rashwinr/WISE/matlab/IEEE_sensors/data_matched/LA,LF,RA,RF/Y/60_down_final.jpg

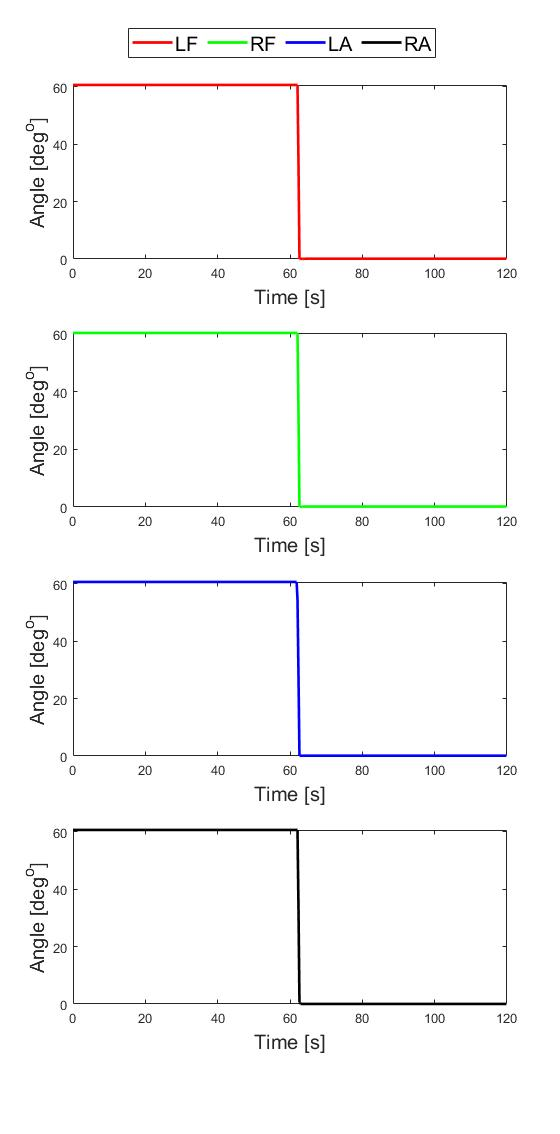
matlab/IEEE_sensors/data_matched/LA,LF,RA,RF/Y/60_down_final.jpg
