rashwinr/WISE/matlab/IEEE_sensors/data_matched/LA,LF,RA,RF/Y/80_up_final.jpg

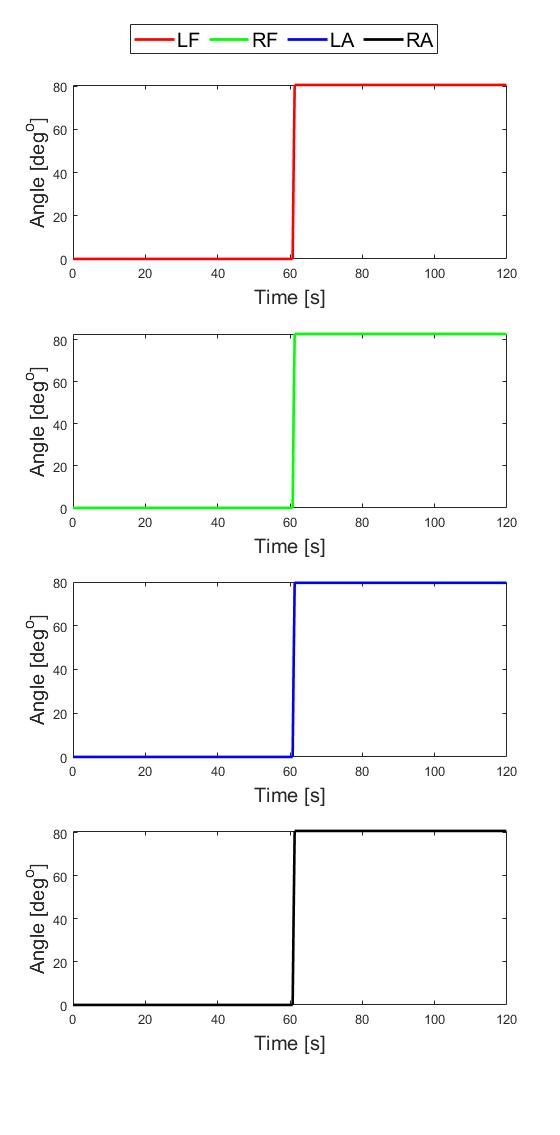
matlab/IEEE_sensors/data_matched/LA,LF,RA,RF/Y/80_up_final.jpg
