rashwinr/WISE/matlab/IEEE_sensors/data_matched/LA,LF,RA,RF/Y/final_0_mp.png

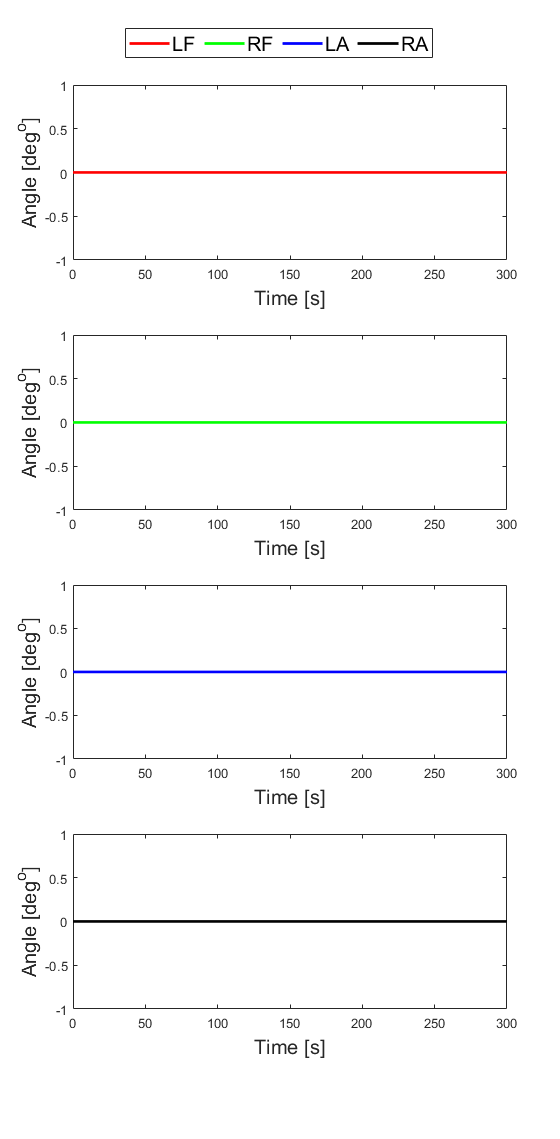
matlab/IEEE_sensors/data_matched/LA,LF,RA,RF/Y/final_0_mp.png
