rashwinr/WISE/matlab/IEEE_sensors/data_matched/LA,LF,RA,RF/Y/final_0degrees.jpg

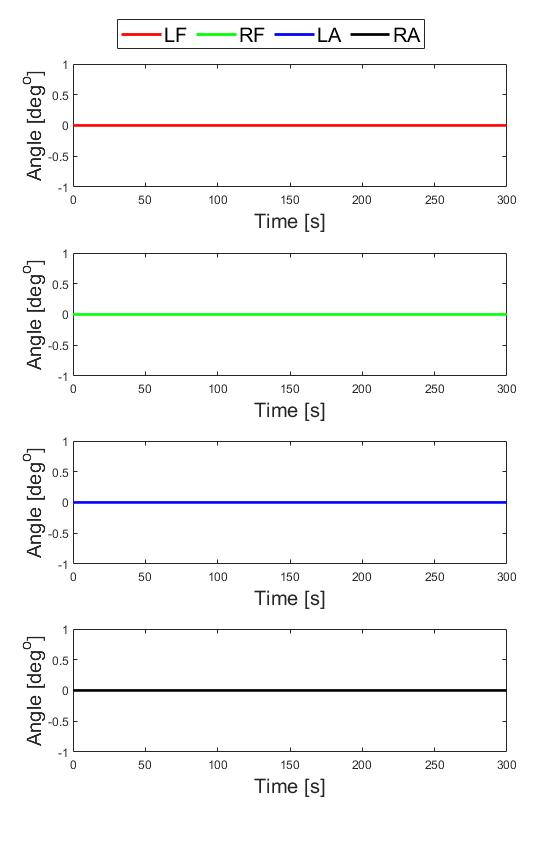
matlab/IEEE_sensors/data_matched/LA,LF,RA,RF/Y/final_0degrees.jpg
