rashwinr/WISE/matlab/IEEE_sensors/data_matched/LA,LF,RA,RF/Y/final_4comments.jpg

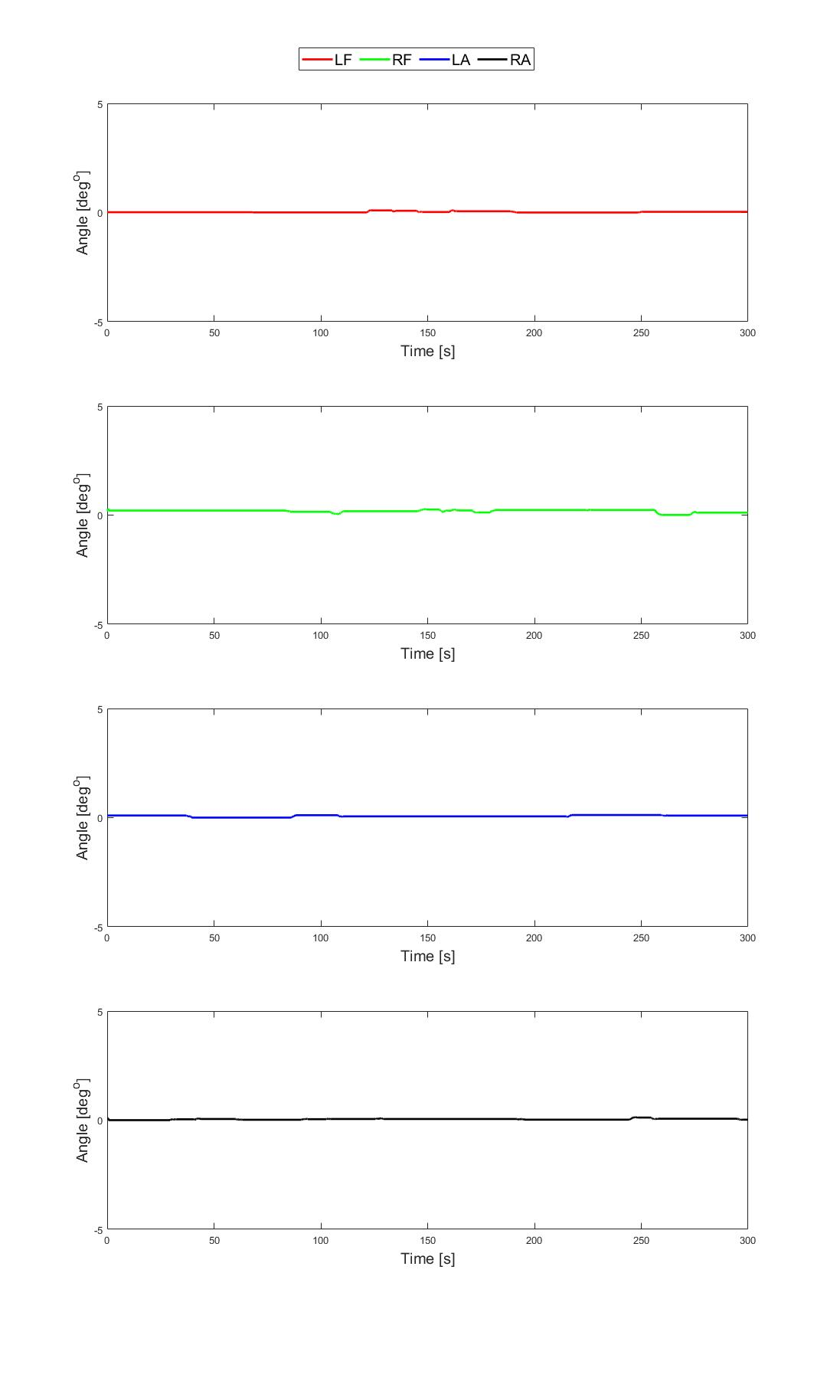
matlab/IEEE_sensors/data_matched/LA,LF,RA,RF/Y/final_4comments.jpg
