rashwinr/WISE/matlab/IEEE_sensors/data_matched/LA,LF,RA,RF/Y/final_4comments_-1to1.jpg

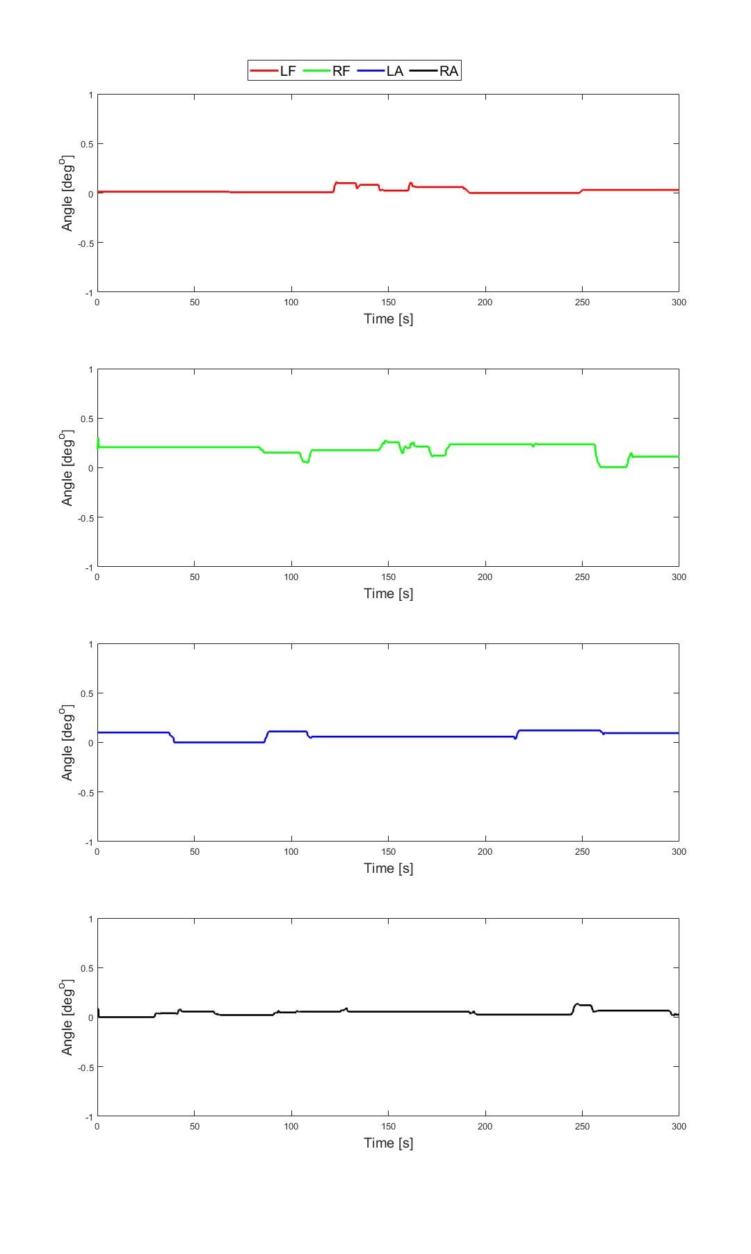
matlab/IEEE_sensors/data_matched/LA,LF,RA,RF/Y/final_4comments_-1to1.jpg
