rashwinr/WISE/matlab/IEEE_sensors/data_matched/LA,LF,RA,RF/Y/o degrees_five mins_better.jpg

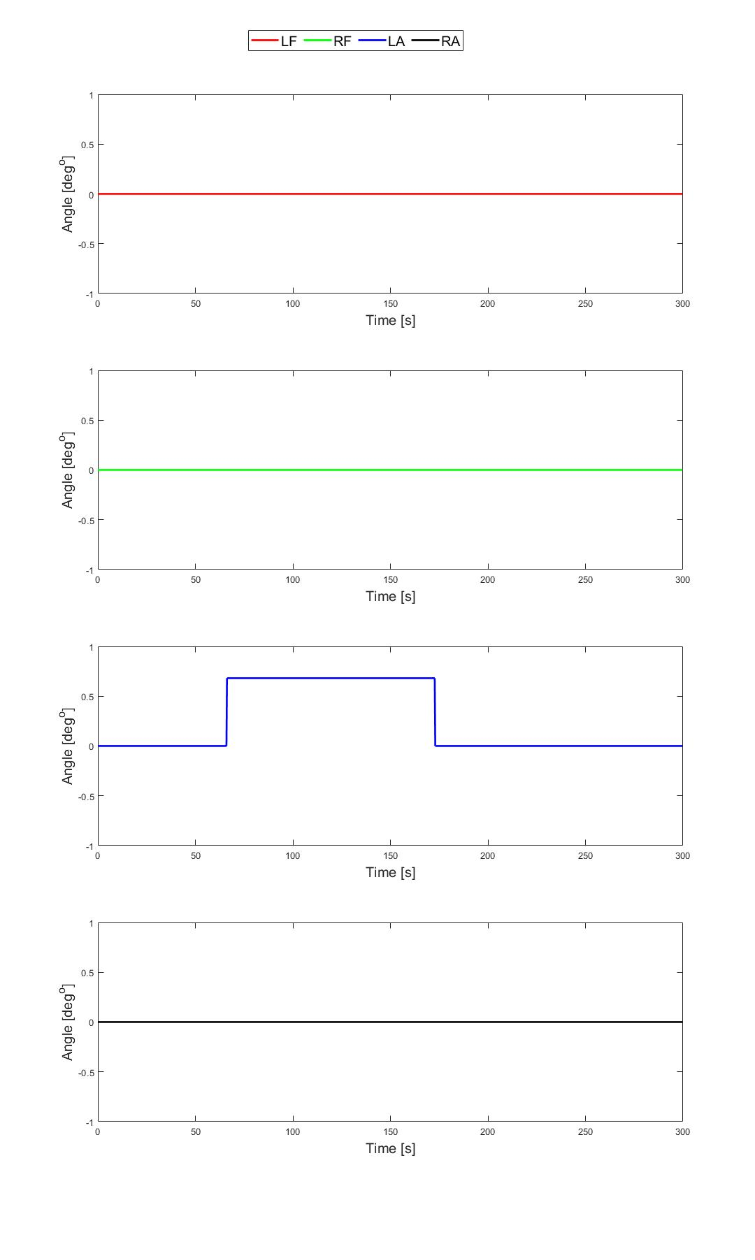
matlab/IEEE_sensors/data_matched/LA,LF,RA,RF/Y/o degrees_five mins_better.jpg
