rashwinr/WISE/matlab/IEEE_sensors/data_matched/LA,LF,RA,RF/Y/stepdown_80_60sectry.jpg

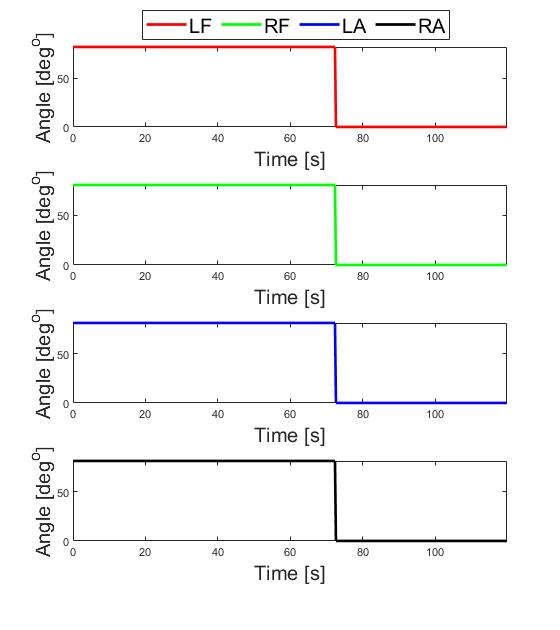
matlab/IEEE_sensors/data_matched/LA,LF,RA,RF/Y/stepdown_80_60sectry.jpg
