rashwinr/WISE/matlab/IEEE_sensors/data_matched/LA,LF,RA,RF/Z/0-90-180.png

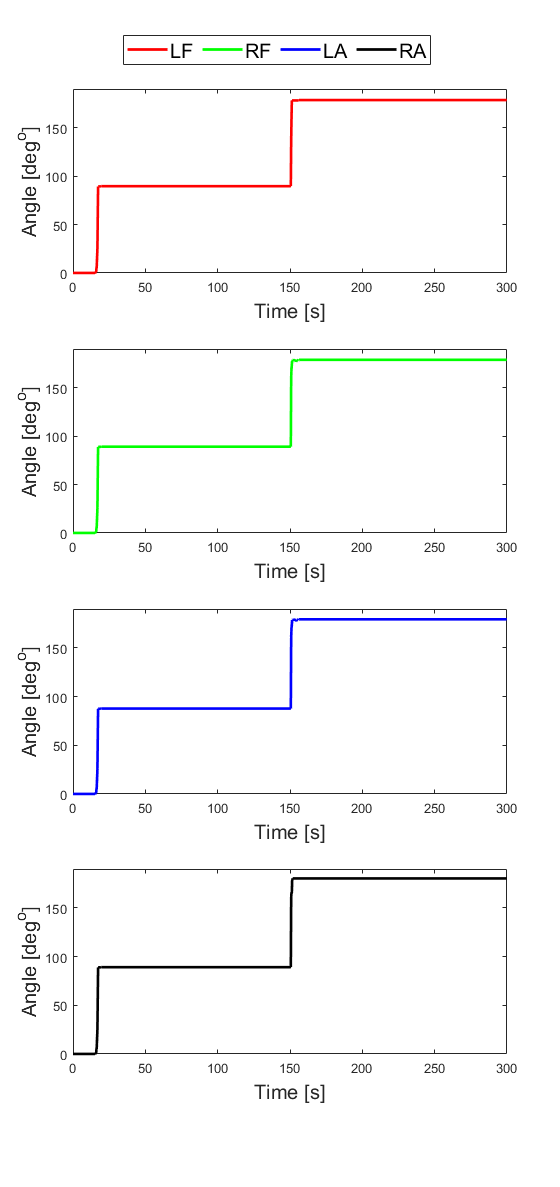
matlab/IEEE_sensors/data_matched/LA,LF,RA,RF/Z/0-90-180.png
