rashwinr/WISE/matlab/IEEE_sensors/data_matched/LA,RA/Y/40 degrees.png

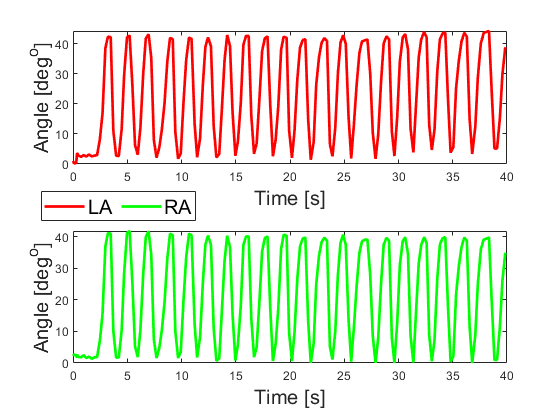
matlab/IEEE_sensors/data_matched/LA,RA/Y/40 degrees.png
