rashwinr/WISE/matlab/IEEE_sensors/data_matched/LA,RA/Y/60 degrees.png

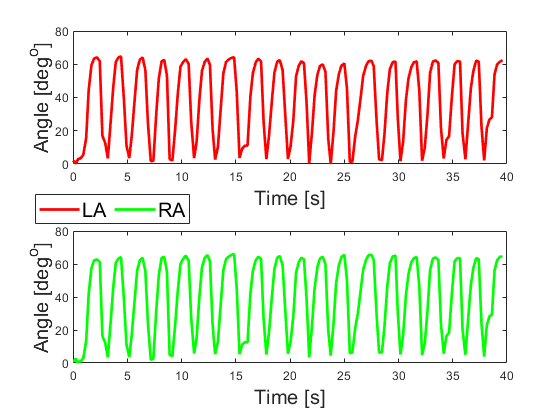
matlab/IEEE_sensors/data_matched/LA,RA/Y/60 degrees.png
