rashwinr/WISE/matlab/IEEE_sensors/data_matched/LA,RA/Y/80 degrees.png

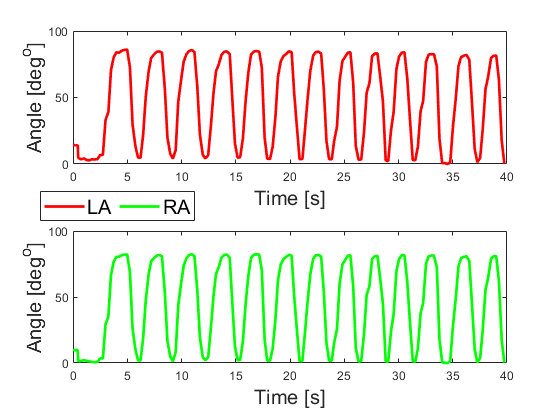
matlab/IEEE_sensors/data_matched/LA,RA/Y/80 degrees.png
