rashwinr/WISE/matlab/IEEE_sensors/data_matched/LF,RF/Y/60 degrees.png

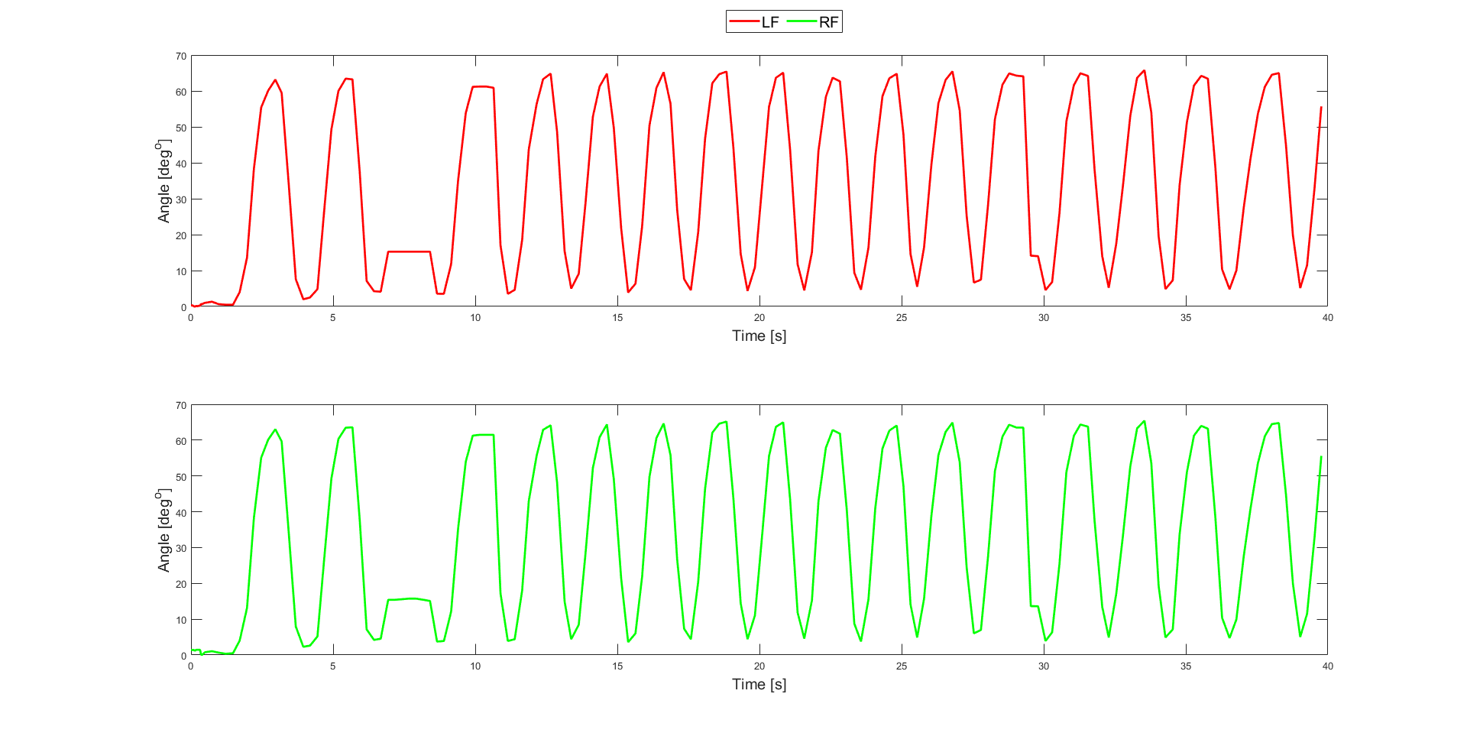
matlab/IEEE_sensors/data_matched/LF,RF/Y/60 degrees.png
