rashwinr/WISE/matlab/IEEE_sensors/data_matched/LF,RF/Y/80 degrees.png

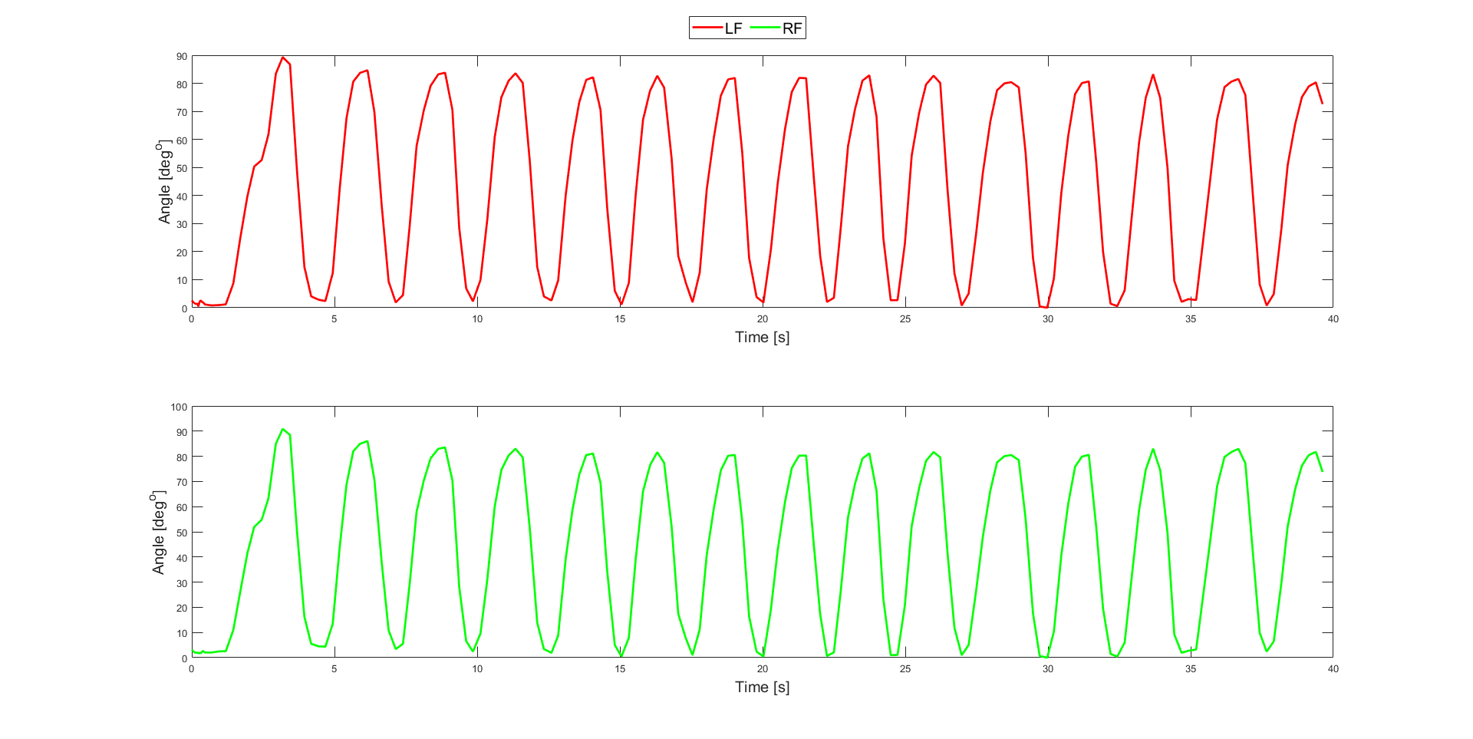
matlab/IEEE_sensors/data_matched/LF,RF/Y/80 degrees.png
