rashwinr/WISE/matlab/IEEE_sensors/data_matched/LF,RF/Z/20 degrees.png

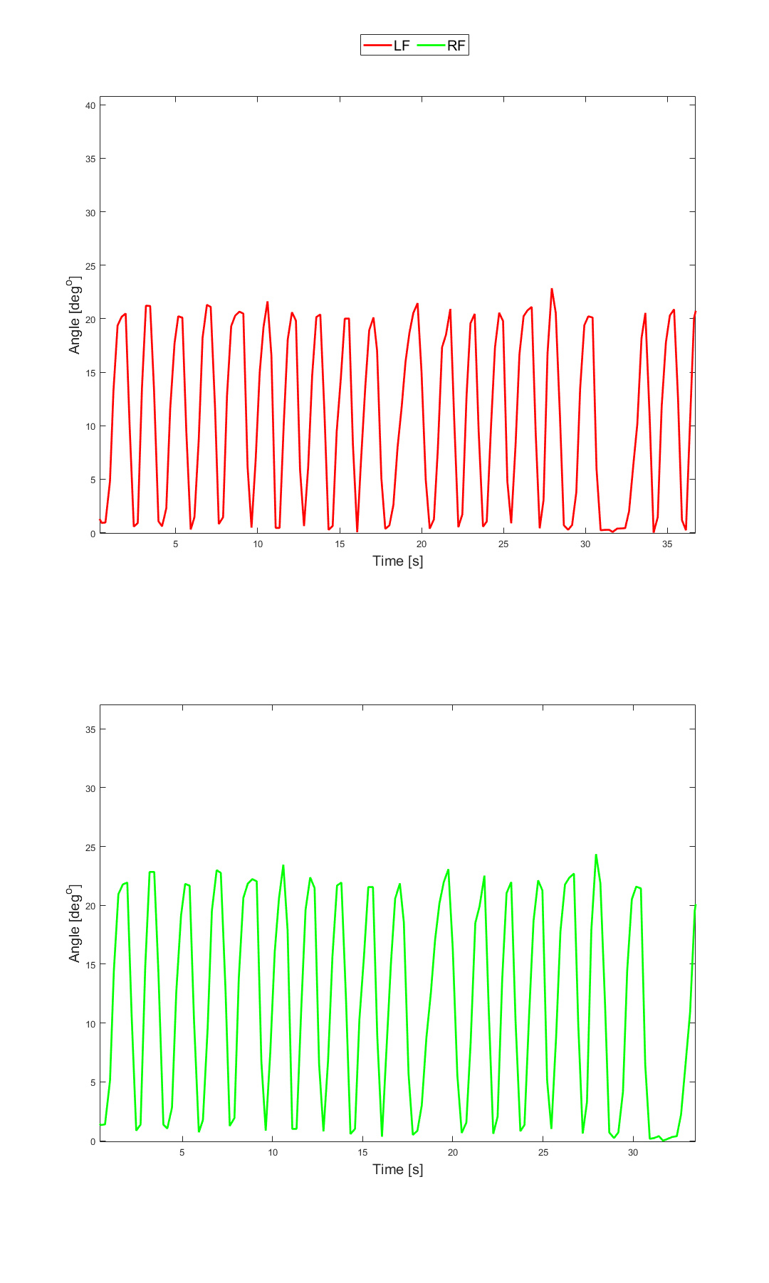
matlab/IEEE_sensors/data_matched/LF,RF/Z/20 degrees.png
