rashwinr/WISE/matlab/IEEE_sensors/data_matched/LF,RF/Z/40 degrees.png

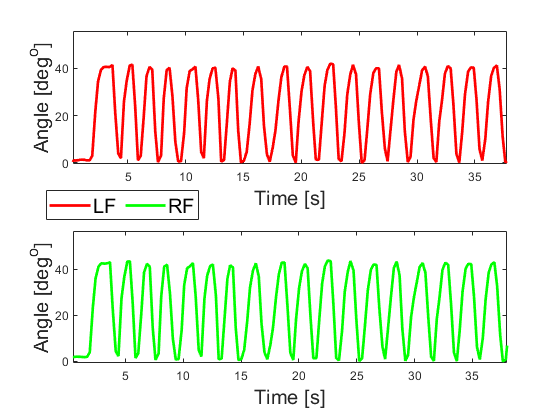
matlab/IEEE_sensors/data_matched/LF,RF/Z/40 degrees.png
