rashwinr/WISE/matlab/IEEE_sensors/data_matched/LF,RF/Z/80 degrees.png

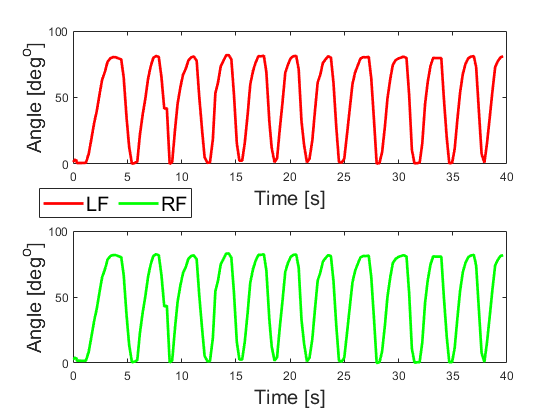
matlab/IEEE_sensors/data_matched/LF,RF/Z/80 degrees.png
