rashwinr/WISE/matlab/IEEE_sensors/JCS_data/instrreset1/lbd_arom.jpg

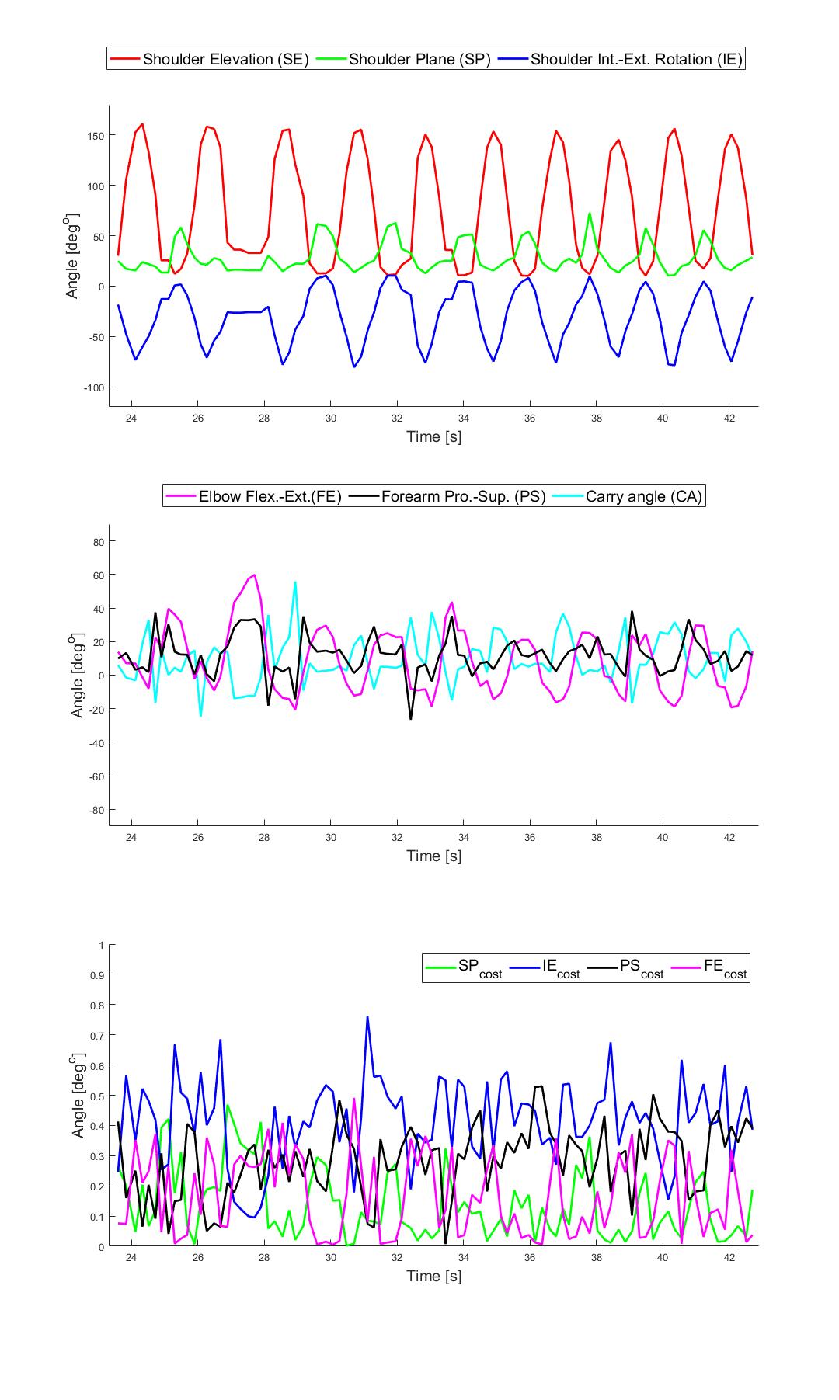
matlab/IEEE_sensors/JCS_data/instrreset1/lbd_arom.jpg
