rashwinr/WISE/matlab/IEEE_sensors/JCS_data/instrreset1/lbd_costsummary.jpg

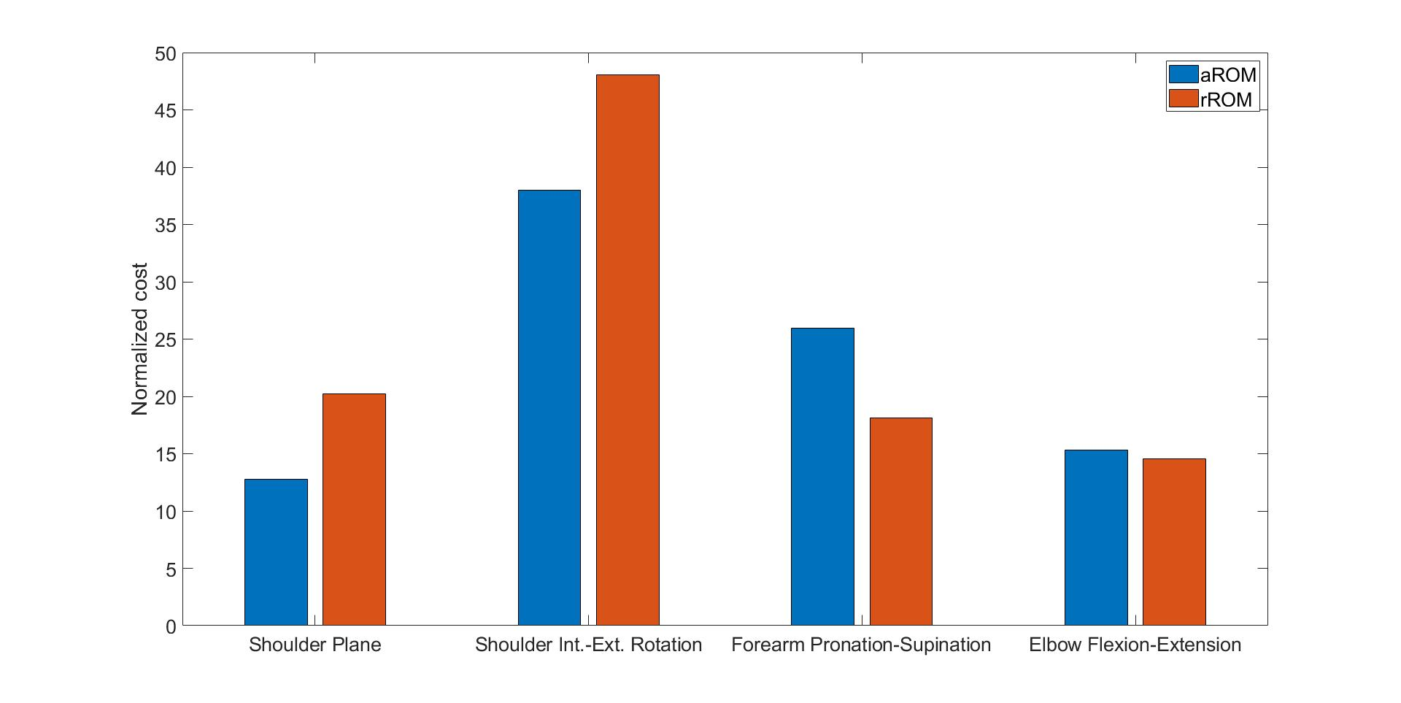
matlab/IEEE_sensors/JCS_data/instrreset1/lbd_costsummary.jpg
