rashwinr/WISE/matlab/IEEE_sensors/JCS_data/instrreset1/lbd_rrom.jpg

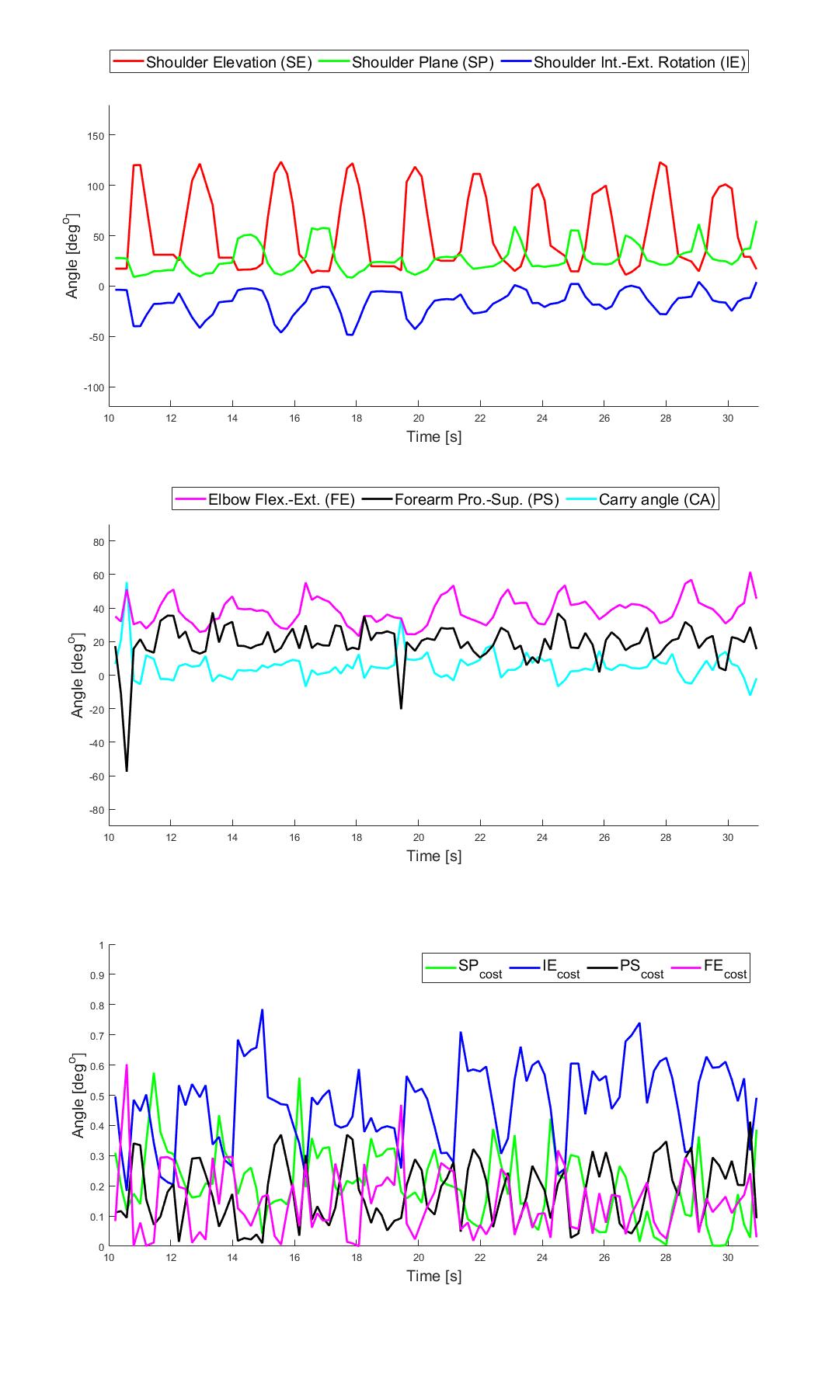
matlab/IEEE_sensors/JCS_data/instrreset1/lbd_rrom.jpg
