rashwinr/WISE/matlab/IEEE_sensors/JCS_data/instrreset1/lfe_arom.jpg

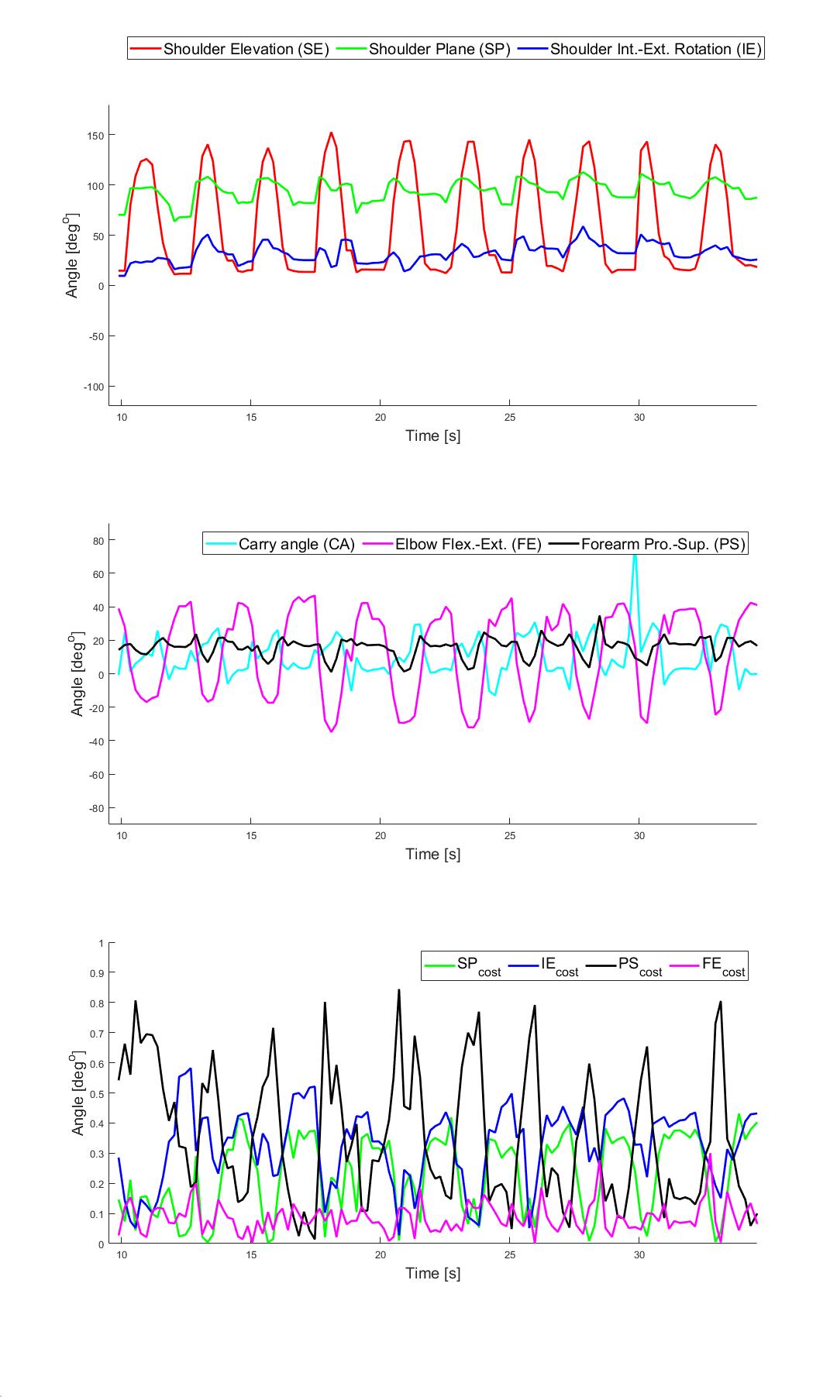
matlab/IEEE_sensors/JCS_data/instrreset1/lfe_arom.jpg
