rashwinr/WISE/matlab/IEEE_sensors/JCS_data/instrreset1/lfe_costsummary.jpg

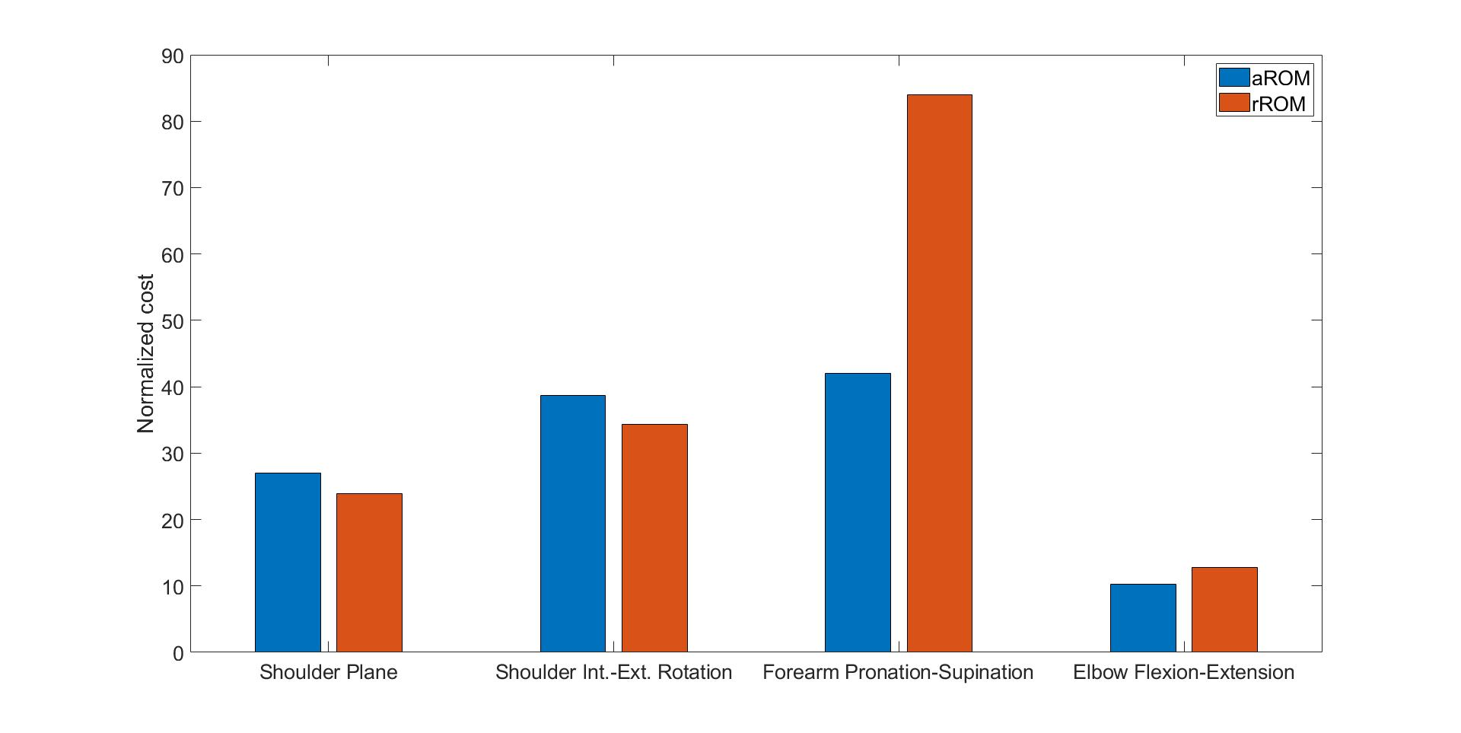
matlab/IEEE_sensors/JCS_data/instrreset1/lfe_costsummary.jpg
