rashwinr/WISE/matlab/IEEE_sensors/JCS_data/instrreset1/lfe_rrom.jpg

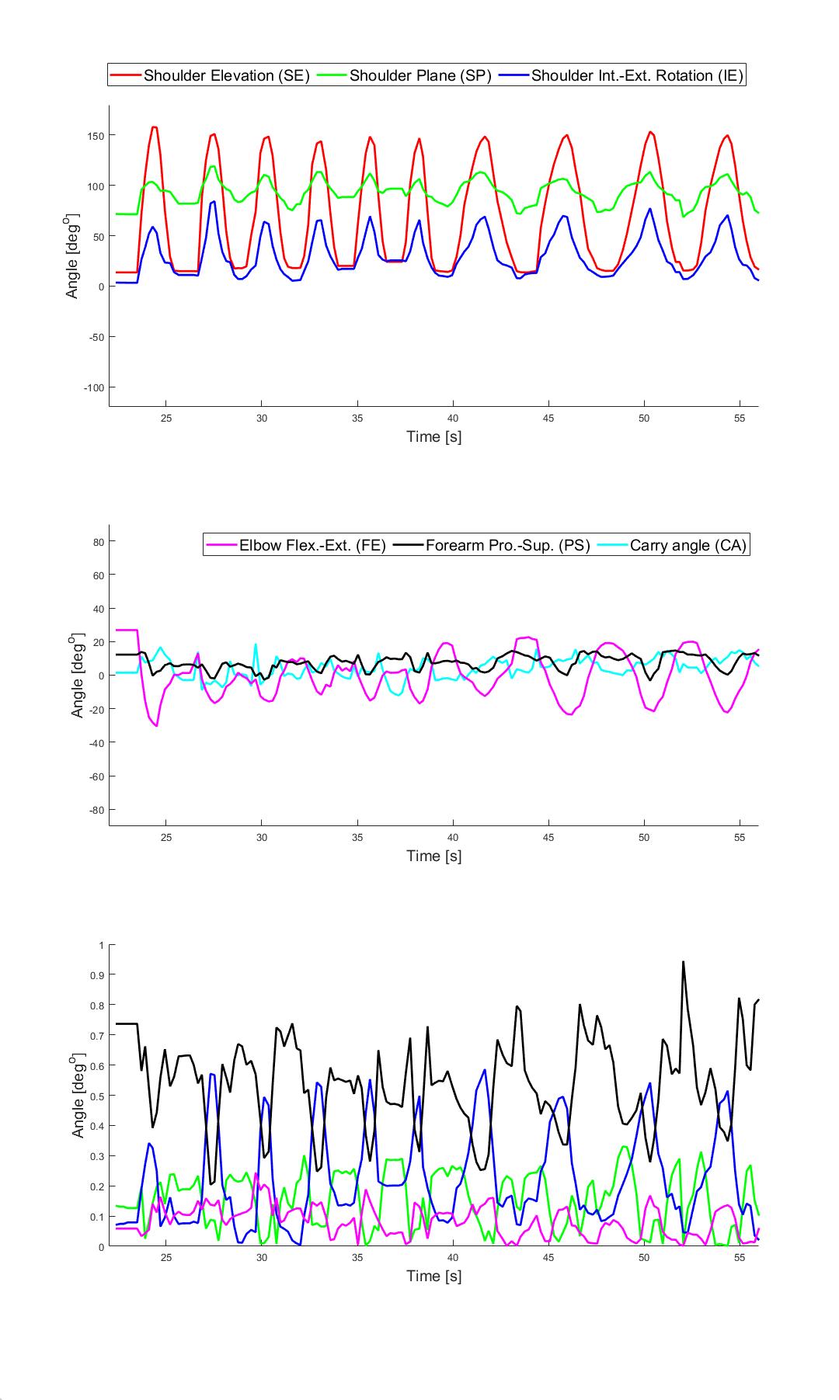
matlab/IEEE_sensors/JCS_data/instrreset1/lfe_rrom.jpg
