rashwinr/WISE/matlab/IEEE_sensors/JCS_data/instrreset/datamodeled_lbd.jpg

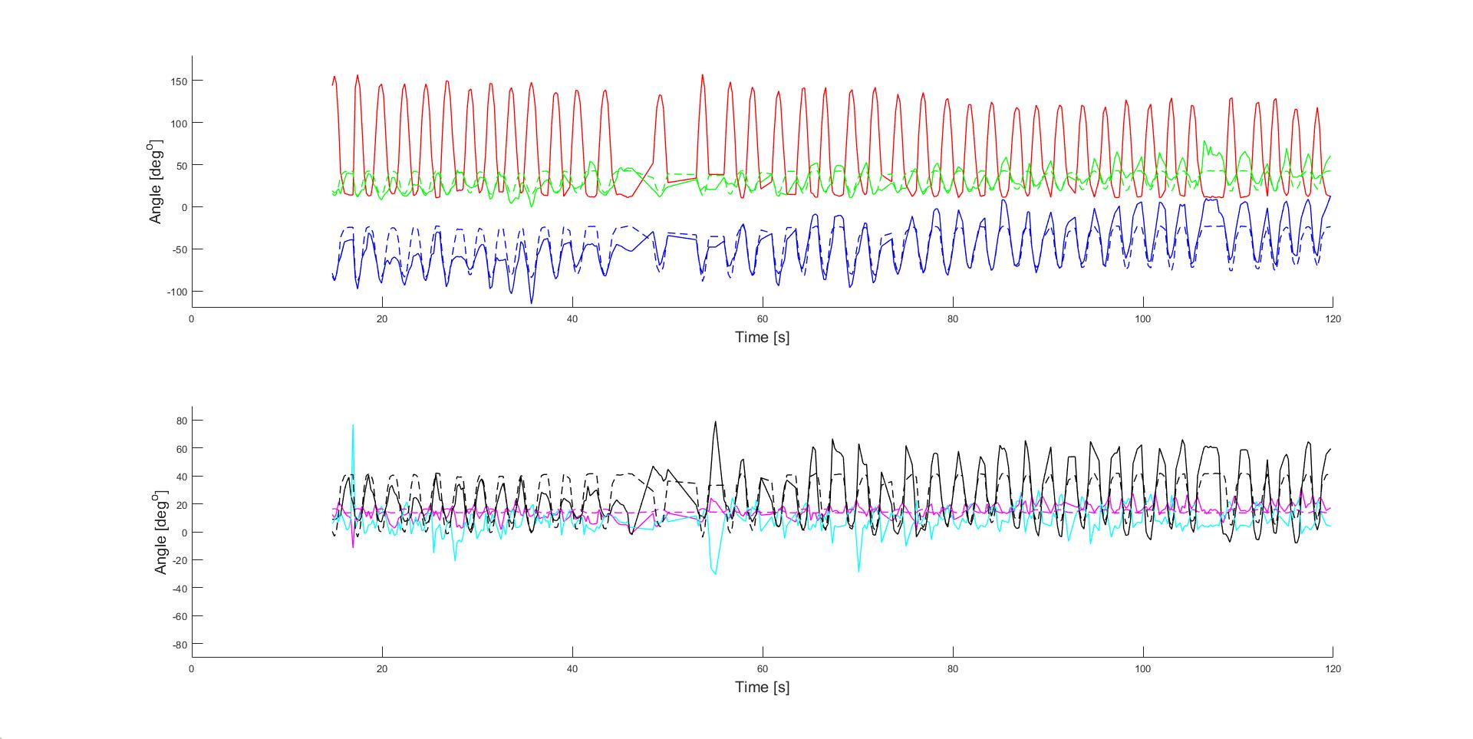
matlab/IEEE_sensors/JCS_data/instrreset/datamodeled_lbd.jpg
