rashwinr/WISE/matlab/IEEE_sensors/JCS_data/instrreset/datamodeling_lbd.jpg

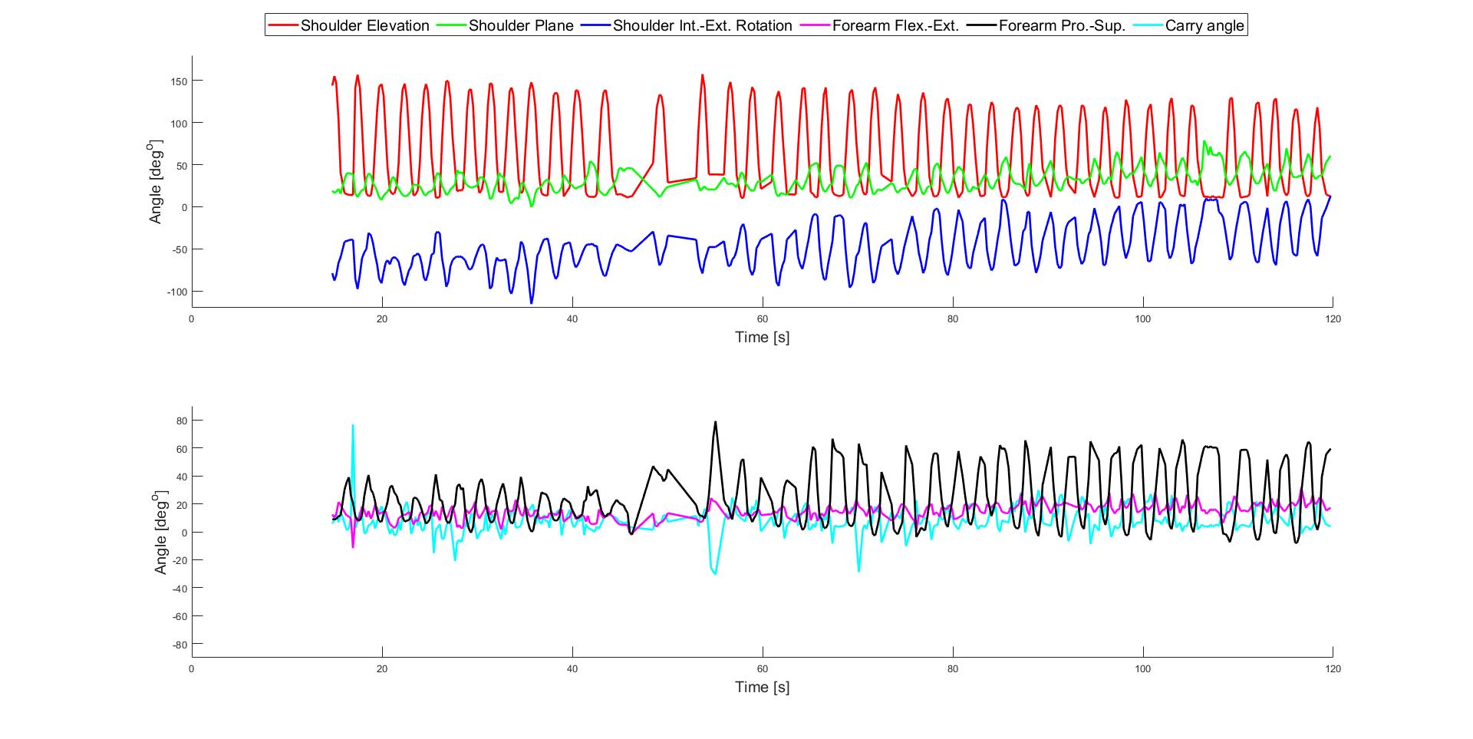
matlab/IEEE_sensors/JCS_data/instrreset/datamodeling_lbd.jpg
