rashwinr/WISE/matlab/IEEE_sensors/JCS_data/instrreset/plot1.jpg

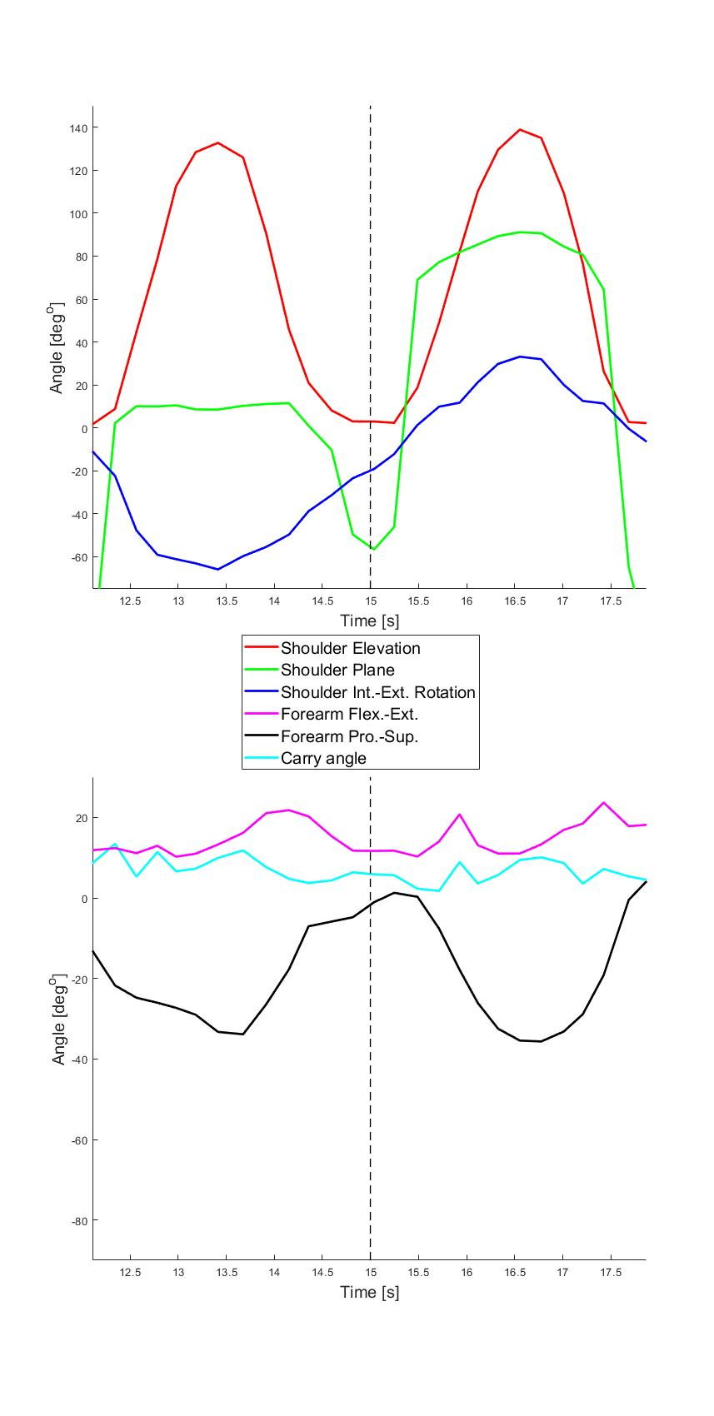
matlab/IEEE_sensors/JCS_data/instrreset/plot1.jpg
