rashwinr/WISE/matlab/IEEE_sensors/JCS_data/Satish/JCS_full time.jpg

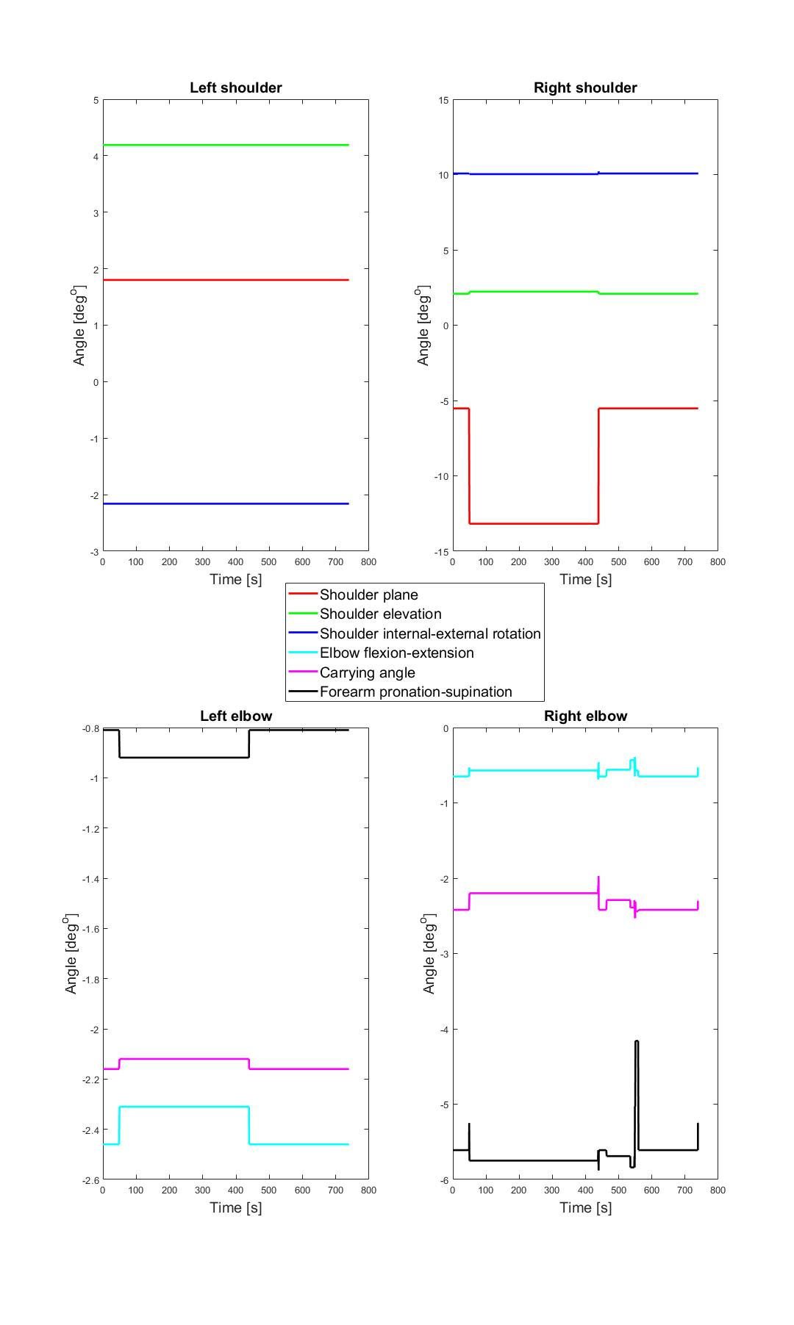
matlab/IEEE_sensors/JCS_data/Satish/JCS_full time.jpg
