rashwinr/WISE/matlab/IEEE_spmb/data_matched/A,B,C,D/Y/40 degress.png

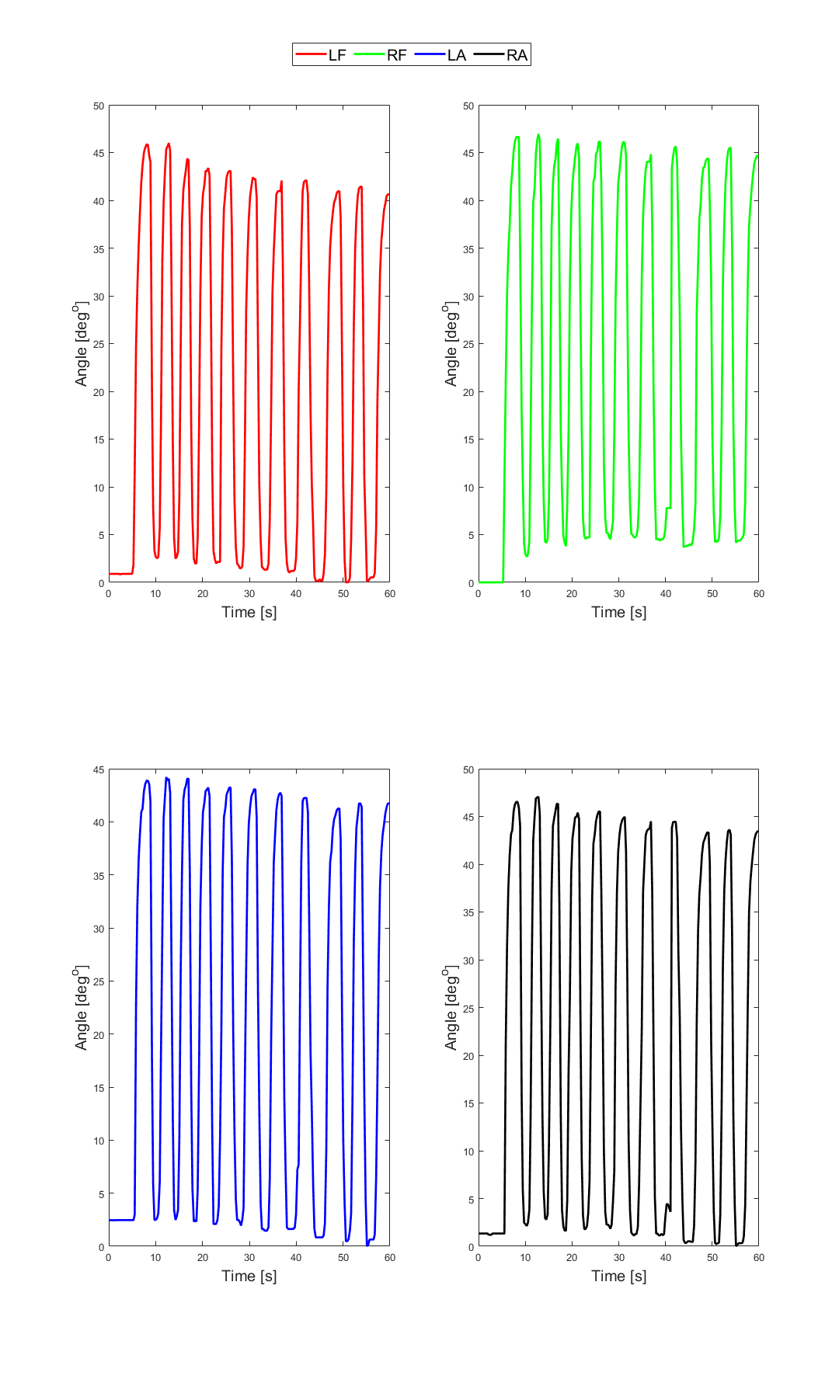
matlab/IEEE_spmb/data_matched/A,B,C,D/Y/40 degress.png
