rashwinr/WISE/matlab/IEEE_spmb/data_matched/A,B,C,D/Z/60 degress.png

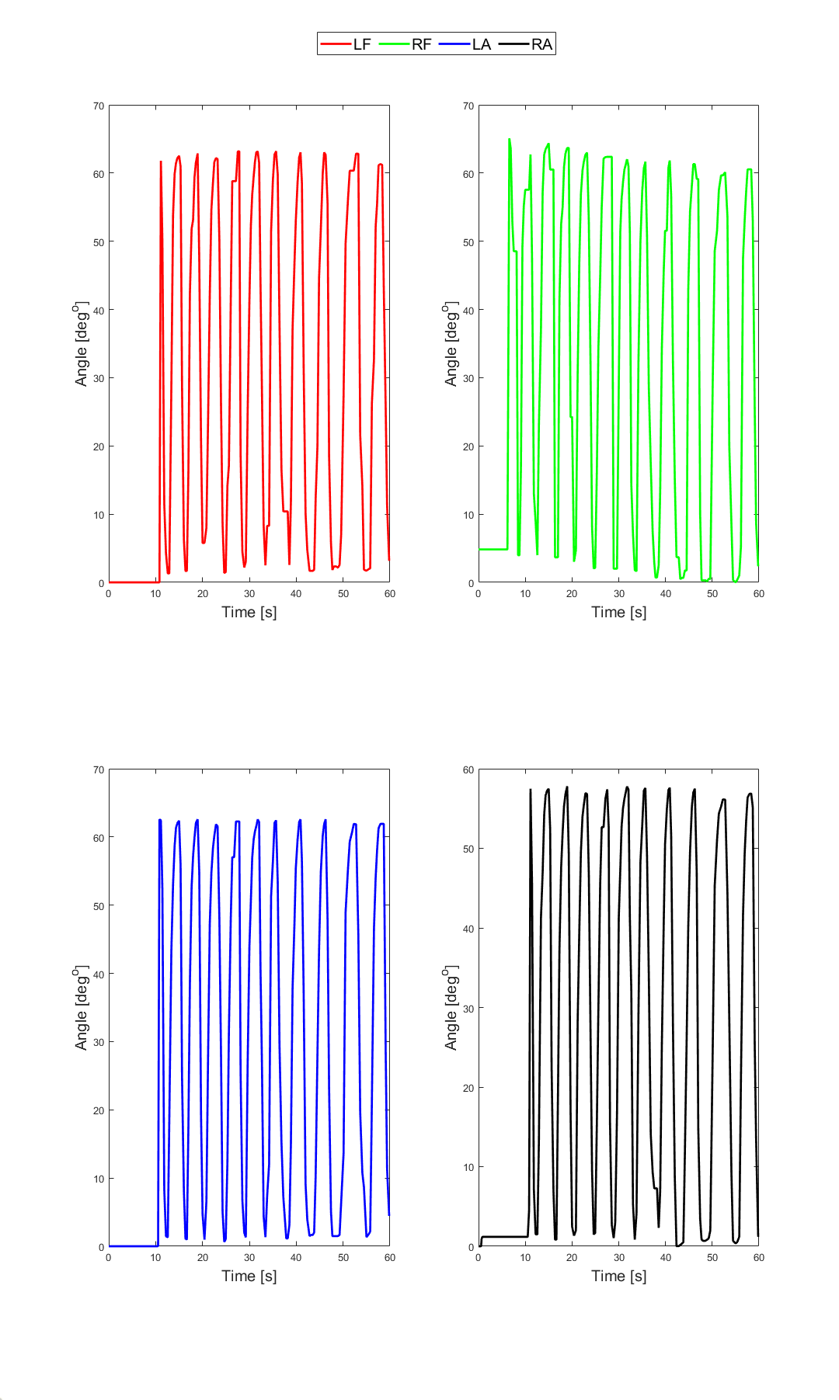
matlab/IEEE_spmb/data_matched/A,B,C,D/Z/60 degress.png
