rashwinr/WISE/matlab/kinect+imudata/RMSE_plots/2064.jpg

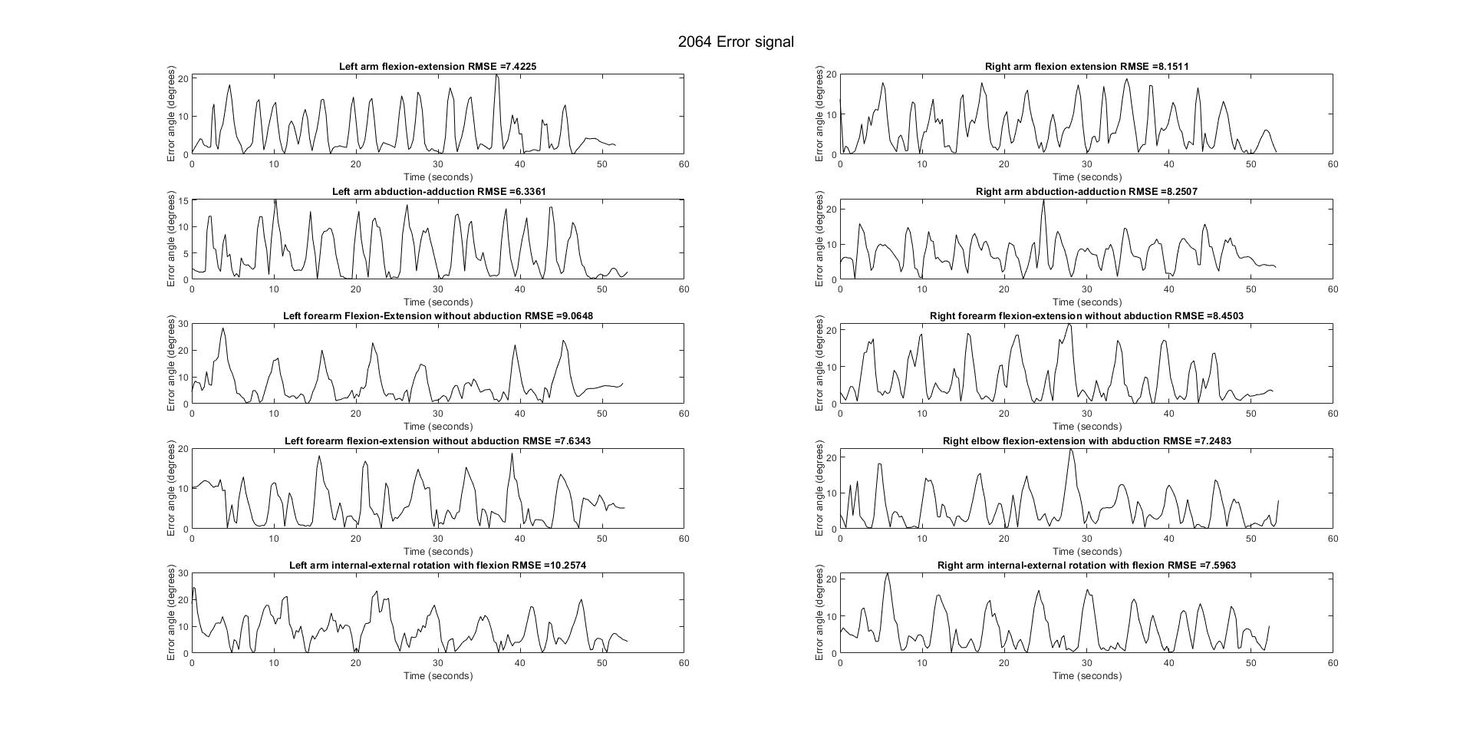
matlab/kinect+imudata/RMSE_plots/2064.jpg
