rashwinr/WISE/matlab/kinect+imudata/RMSE_plots/7612.jpg

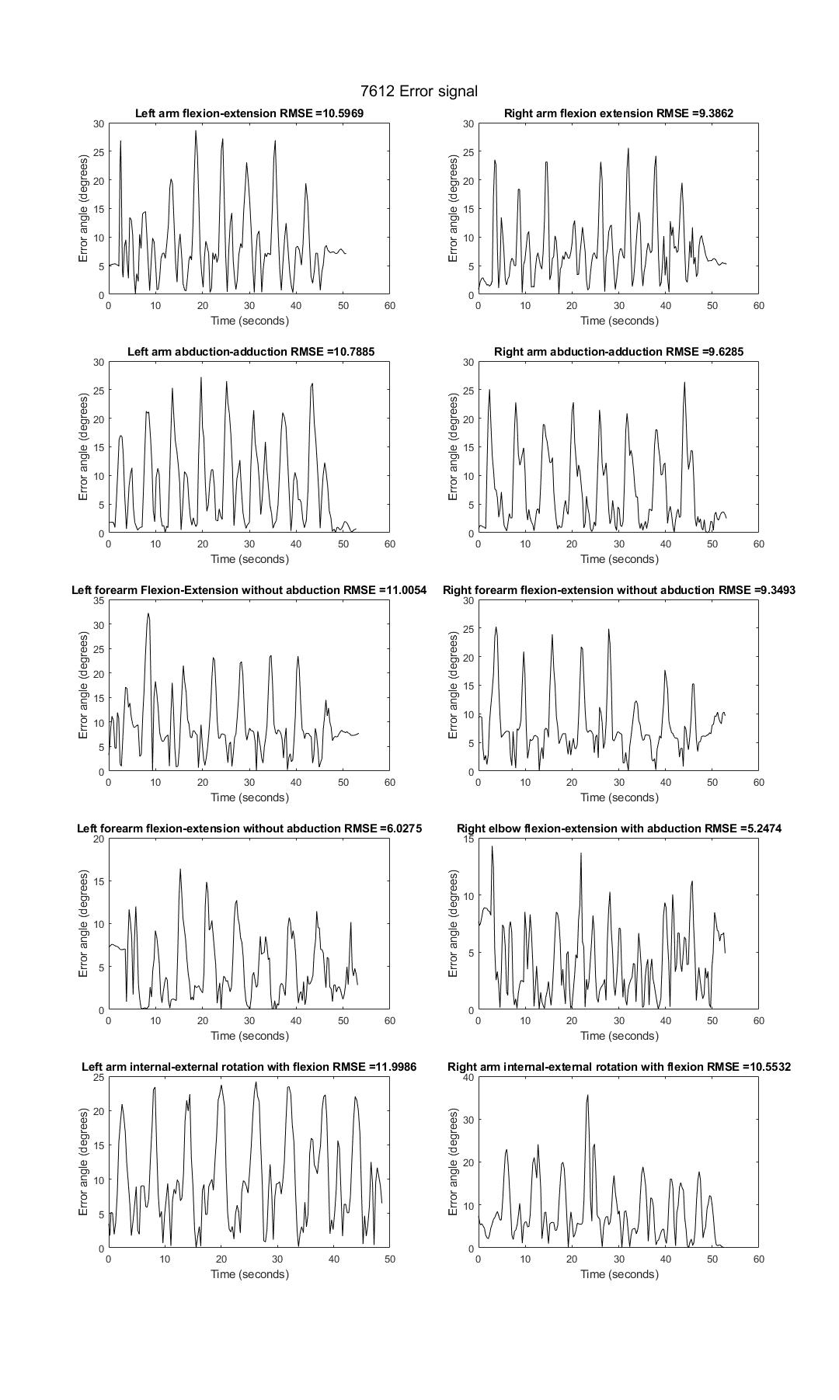
matlab/kinect+imudata/RMSE_plots/7612.jpg
