rashwinr/WISE/3D model/top_part_12_14_2018.SLDPRT

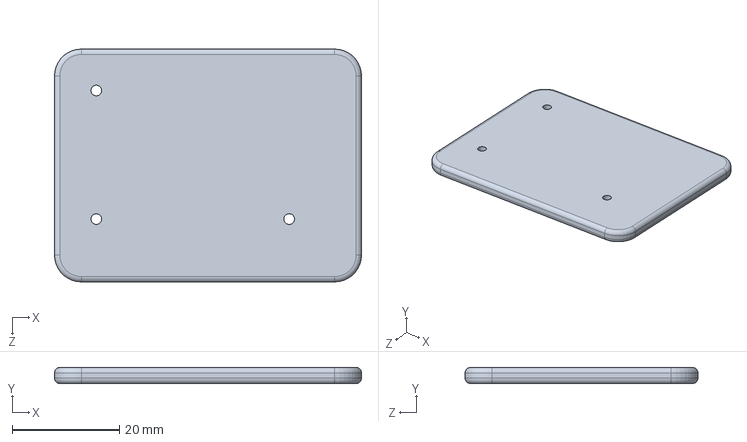
[picture p51: CAD file, 2019-02-20]
3D model/top_part_12_14_2018.SLDPRT
57.3 x 3.00 x 43.5 mm
