rashwinr/WISE/STL_4/WISE_design/H_holder.stl

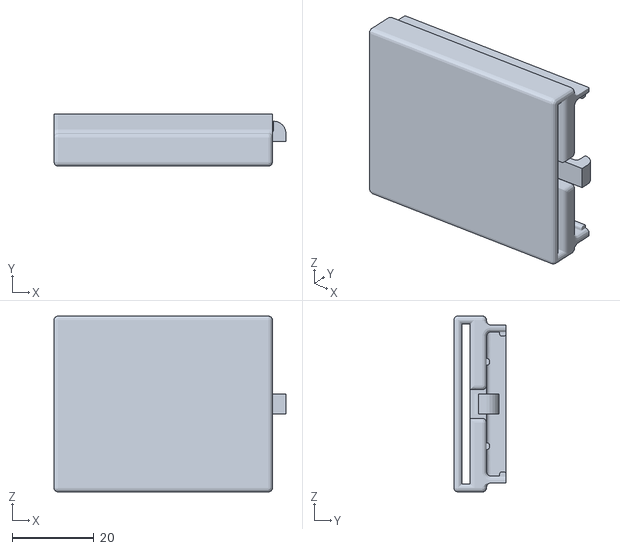
[picture p52: CAD file, 2019-06-13]
STL_4/WISE_design/H_holder.stl
56.7 x 12.8 x 43.0
