rashwinr/WISE/STL_4/WISE_design/V_holder.stl

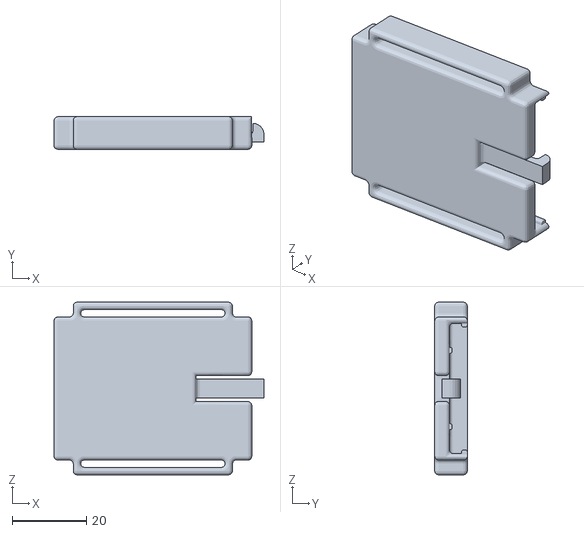
[picture p53: CAD file, 2019-06-13]
STL_4/WISE_design/V_holder.stl
56.7 x 8.80 x 46.6
