rashwinr/WISE/matlab/IEEE_sensors/data_matched/LA,LF,RA,RF/Y/step down_80.jpg

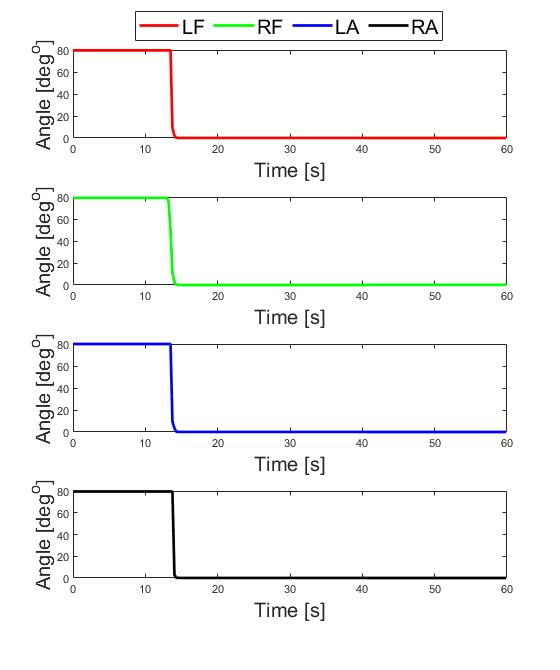
matlab/IEEE_sensors/data_matched/LA,LF,RA,RF/Y/step down_80.jpg
