rashwinr/WISE/matlab/IEEE_sensors/data_matched/LA,LF,RA,RF/Y/step down_80_1.jpg

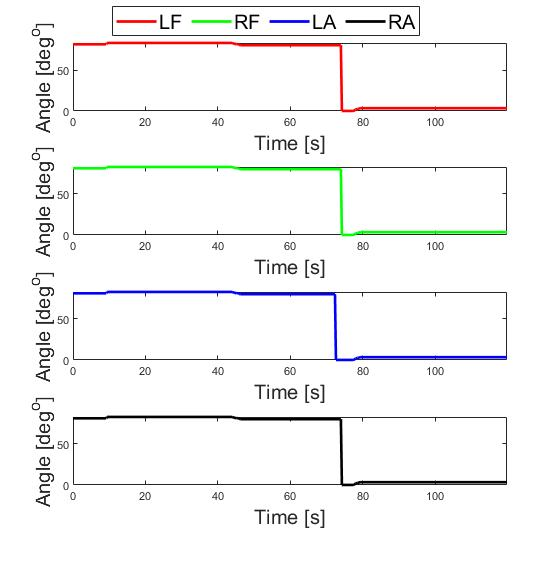
matlab/IEEE_sensors/data_matched/LA,LF,RA,RF/Y/step down_80_1.jpg
