rashwinr/WISE/matlab/IEEE_sensors/data_matched/LA,LF,RA,RF/Y/step up.png

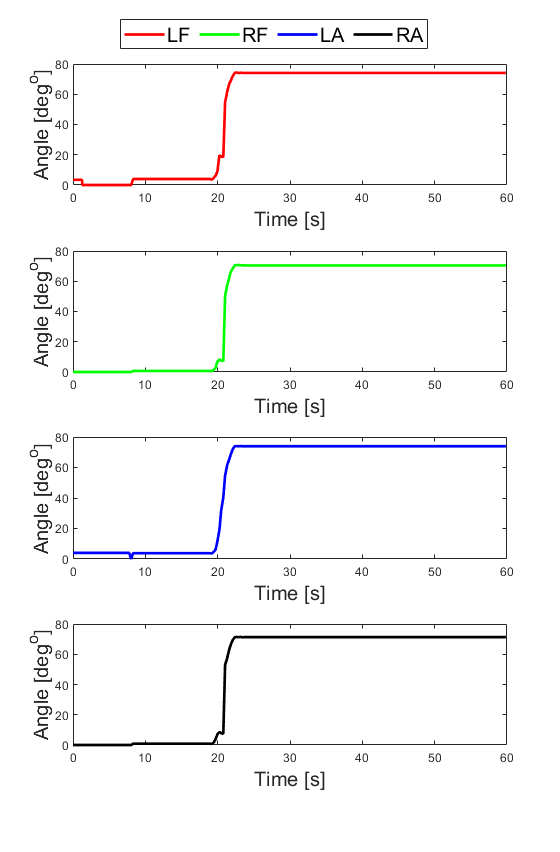
matlab/IEEE_sensors/data_matched/LA,LF,RA,RF/Y/step up.png
