rashwinr/WISE/matlab/IEEE_sensors/data_matched/LA,LF,RA,RF/Y/step up_60.jpg

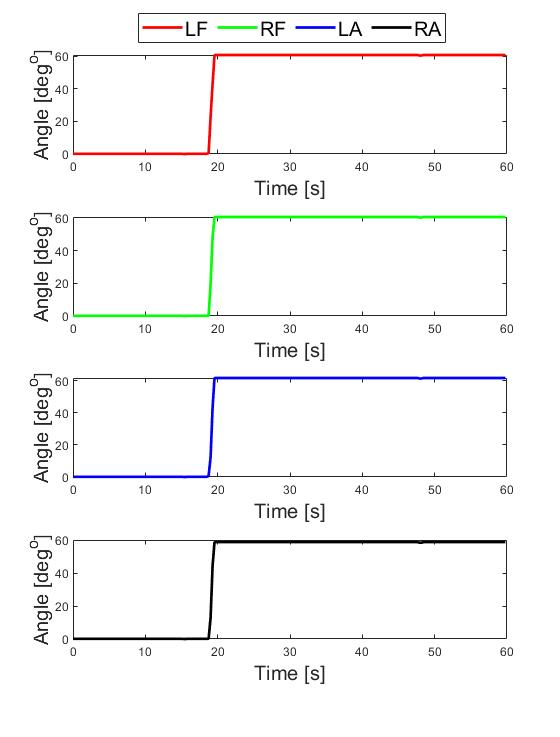
matlab/IEEE_sensors/data_matched/LA,LF,RA,RF/Y/step up_60.jpg
